piotrvvilk/kaloszek/epd_iconpack.h

// 'bw_1', 55x55px
const unsigned char weatherIco1 [] PROGMEM = {
	0x00, 0x00, 0x00, 0x10, 0x00, 0x00, 0x00, 0x00, 0x00, 0x00, 0x38, 0x00, 0x00, 0x00, 0x00, 0x00, 
	0x00, 0x38, 0x00, 0x00, 0x00, 0x00, 0x00, 0x00, 0x38, 0x00, 0x00, 0x00, 0x00, 0x00, 0x00, 0x38, 
	0x00, 0x00, 0x00, 0x00, 0x00, 0x00, 0x38, 0x00, 0x00, 0x00, 0x00, 0x00, 0x00, 0x38, 0x00, 0x00, 
	0x00, 0x00, 0x00, 0x00, 0x38, 0x00, 0x00, 0x00, 0x00, 0xc0, 0x00, 0x18, 0x00, 0x06, 0x00, 0x00, 
	0xe0, 0x00, 0x00, 0x00, 0x0e, 0x00, 0x00, 0x70, 0x00, 0x00, 0x00, 0x1c, 0x00, 0x00, 0x38, 0x00, 
	0x00, 0x00, 0x38, 0x00, 0x00, 0x1c, 0x03, 0xff, 0x80, 0x70, 0x00, 0x00, 0x0e, 0x0f, 0xff, 0xe0, 
	0xe0, 0x00, 0x00, 0x06, 0x3e, 0x00, 0xf8, 0x40, 0x00, 0x00, 0x00, 0x78, 0x00, 0x3c, 0x00, 0x00, 
	0x00, 0x00, 0xe0, 0x00, 0x0e, 0x00, 0x00, 0x00, 0x01, 0xc0, 0x00, 0x07, 0x00, 0x00, 0x00, 0x03, 
	0x80, 0x00, 0x03, 0x80, 0x00, 0x00, 0x03, 0x00, 0x00, 0x01, 0x80, 0x00, 0x00, 0x07, 0x00, 0x00, 
	0x01, 0xc0, 0x00, 0x00, 0x06, 0x00, 0x00, 0x00, 0xc0, 0x00, 0x00, 0x0e, 0x00, 0x00, 0x00, 0xe0, 
	0x00, 0x00, 0x0c, 0x00, 0x00, 0x00, 0x60, 0x00, 0x00, 0x0c, 0x00, 0x00, 0x00, 0x60, 0x00, 0x00, 
	0x0c, 0x00, 0x00, 0x00, 0x60, 0x00, 0x7f, 0x8c, 0x00, 0x00, 0x00, 0x71, 0xfc, 0xff, 0x8c, 0x00, 
	0x00, 0x00, 0x73, 0xfe, 0x7f, 0x0c, 0x00, 0x00, 0x00, 0x71, 0xfc, 0x00, 0x0c, 0x00, 0x00, 0x00, 
	0x60, 0x00, 0x00, 0x0c, 0x00, 0x00, 0x00, 0x60, 0x00, 0x00, 0x0c, 0x00, 0x00, 0x00, 0x60, 0x00, 
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
	0x1e, 0x67, 0x06, 0x64, 0x00, 0x00, 0x60, 0x18, 0x63, 0x00, 0x60, 0x00, 0x00, 0x60, 0x00, 0x60, 
	0x00, 0x60, 0x00, 0x00, 0x00, 0x00, 0x60, 0x00, 0x00, 0x00, 0x00, 0x00, 0x00, 0x60, 0x00, 0x00, 
	0x00
};
