piotrvvilk/kaloszek/authentication.h

//=========================================================================================================================================== wifi
const char* ssid_1 = "xxxx";              //your wifi_1 ssid
const char* password_1 = "xxxx";          //your wifi_1 password

const char* ssid_2 = "xxxx";              //your wifi_2 ssid 
const char* password_2 = "xxxx";          //your wifi_1 password

//=========================================================================================================================================== accuweather keys
const char acu_keys[][33] = 
{
  "key_1",                                //your accuweather keys        
  "key_2",
  "key_3",
  "key_4"
};
